HMGrunthos/CapInrushLimiter/CapInrush5-30V.asc

B1: bv; V=V(RCA,RCB)
C2: cap; 13200µF; V=50 Rser=0.03
C3: cap; 13200µF; V=50 Rser=0.03
C6: cap; 100nF; V=60
C7: cap; 100e-6
C10: cap; 16200µF; V=80 Rser=0.016
C11: cap; 680e-9
C12: cap; 10e-6
D1: diode; UF5406
D2: zener; BZX84B9V1LY
D3: zener; bzx55c24
D4: schottky; RB238NS150
D5: diode; BAS16H
D6: schottky; RB238NS150
D7: schottky; RB238NS150
D8: schottky; RB238NS150
D9: schottky; RB238NS150
D10: schottky; RB238NS150
D11: schottky; RB238NS150
D12: schottky; RB238NS150
D13: zener; BZX84B9V1LY
D14: diode; BAS16H
D15: diode; BAS16H
D19: zener; BZX84C15L
I1: current; PWL(0 0 4 0 9 7)
L2: ind; 1e-6; Rser=1600
M1: pmos; irf9540npbf
M4: pmos; BSP230
Q2: npn; KST42
Q3: npn; TIP41C
R1: res; R=if(time<0.1,1e9,1e-6)
R3: res; 37.36
R4: res; 0.0855
R5: res; 0.0855
R6: res; 0.0855
R7: res; 0.0855
R9: res; 10e3
R10: res; 8.3e3
R11: res; 43e3
R12: res; 100e3
R15: res; 3.5e3
R17: res; 100e3
R20: res; R=if((time<0.1)|((time > 3.5)&(time<4.5)),1e9,1e-6)
S1: sw; Relay
U1: LM4041_N_ADJ
V2: voltage; SINE(0 37.7736 50 0 0 0 2000)
V3: voltage; SINE(0 37.7736 50 0 0 0 2000)
Named nets: 0, T, S, RCA, RCB
.tran 0 10 0.102 startup
.model UF5406 d(is = 1.15563E-005 n = 3.45 rs = 0.0887337 eg = 1.11 xti = 3 cjo = 9.14327E-011 vj = 0.298558 m = 0.347605 fc = 0.5  tt = 1.57227E-007 bv = 660 ibv = 0.3 af = 1 kf = 0)
.inc Infineon-Spice-File-IRF9540NPBF-SM-v01_00-EN.spi
.options cshunt=1e-15
.inc BAS16H.txt
.inc BSP230.prm
.model Relay SW(Roff=1Meg Ron=1e-3 Vt=18V Vh=1)
.lib KST42.lib
.inc LM4041_N_ADJD1P233_TRANS.lib
.MODEL TIP41C NPN (IS=7.55826e-11 BF=260.542 NF=1.11221 VAF=100 IKF=0.526814
+ISE=1e-08 NE=2.18072 BR=26.0542 NR=1.5 VAR=1000 IKR=3.54059 ISC=1e-08
+NC=1.63849 RB=4.56157 IRB=0.1 RBM=0.1 RE=0.0162111 RC=0.0810556 XTB=0.1
+XTI=1 EG=1.206 CJE=1.93296e-10 VJE=0.4 MJE=0.259503 TF=1e-08 XTF=4.06972
+VTF=7.1157 ITF=0.001 CJC=1.09657e-10 VJC=0.730921 MJC=0.23 XCJC=0.803085 
+FC=0.8 TR=9.01013e-08 PTF=0 Vceo=100 ICrating=6 mfg=ON_Semi)
.lib BZX55C24.lib
