HMGrunthos/CapInrushLimiter/CapInrush5.asc

B1: bv; V=V(RCA,RCB)
C2: cap; 13200µF; V=50 Rser=0.03
C3: cap; 13200µF; V=50 Rser=0.03
C5: cap; 100e-9
C7: cap; 10e-6
C10: cap; 16200µF; V=80 Rser=0.016
C11: cap; 680e-9
C12: cap; 10e-6
D1: diode; UF5406
D2: zener; BZX84B9V1LY
D3: diode; 1N4001
D4: schottky; RB238NS150
D5: diode; BAS16H
D6: schottky; RB238NS150
D7: schottky; RB238NS150
D8: schottky; RB238NS150
D9: schottky; RB238NS150
D10: schottky; RB238NS150
D11: schottky; RB238NS150
D12: schottky; RB238NS150
D13: zener; BZX84B9V1LY
D14: diode; BAS16H
D15: diode; BAS16H
D19: zener; BZX84C15L
D21: LED; REDLED
I1: current; PWL(0 0 4.5 0 9 7)
L2: ind; 1e-6; Rser=5760
M1: pmos; irf9540npbf
M4: pmos; BSP230
Q2: npn; KST42
Q3: npn; KST42
R1: res; R=if(time<0.1,1e9,1e-6)
R3: res; 100
R4: res; 0.0855
R5: res; 0.0855
R6: res; 0.0855
R7: res; 0.0855
R9: res; 100e3
R10: res; 8.3e3
R11: res; 100e3
R12: res; 200e3
R13: res; 1.5e3
R15: res; 3.5e3
R17: res; 100e3
R20: res; R=if((time<0.1)|((time > 3.5)&(time<4.5)),1e9,1e-6)
S1: sw; Relay
V2: voltage; SINE(0 37.7736 50 0 0 0 2000)
V3: voltage; SINE(0 37.7736 50 0 0 0 2000)
Named nets: 0, T, S, RCA, RCB
.tran 10 startup
.model UF5406 d(is = 1.15563E-005 n = 3.45 rs = 0.0887337 eg = 1.11 xti = 3 cjo = 9.14327E-011 vj = 0.298558 m = 0.347605 fc = 0.5  tt = 1.57227E-007 bv = 660 ibv = 0.3 af = 1 kf = 0)
.inc Infineon-Spice-File-IRF9540NPBF-SM-v01_00-EN.spi
.options cshunt=1e-15
.inc BAS16H.txt
.inc BSP230.prm
.model 1N4001 D(Is=14.11n N=1.984 Rs=33.89m Ikf=94.81 Xti=3 Eg=1.11 Cjo=25.89p M=.44 Vj=.3245 Fc=.5 Bv=75 Ibv=10u Tt=5.7u Iave=1 Vpk=50 mfg=GI type=silicon
.model Relay SW(Roff=1Meg Ron=1e-3 Vt=34V Vh=2)
.lib KST42.lib
.MODEL REDLED D (IS=93.2P RS=42M N=3.73 BV=4 IBV=10U CJO=2.97P VJ=.75 M=.333 TT=4.32U)
