HMGrunthos/CapInrushLimiter/CapInrush1.asc

C1: cap; 16200µF; V=80
C2: cap; 10e-6
C3: cap; 680e-9
C4: cap; 13200µF; V=50
C5: cap; 13200µF; V=50
C6: cap; 100nF; V=60
D2: diode; BAS16H
D4: schottky; RB238NS150
D6: schottky; RB238NS150
D7: schottky; RB238NS150
D8: schottky; RB238NS150
D9: schottky; RB238NS150
D10: schottky; RB238NS150
D11: schottky; RB238NS150
D12: schottky; RB238NS150
D13: diode; 1N4001
D14: zener; NZX3V9C
D15: zener; NZX5V6C
D16: zener; BZX84C15L
L1: ind; 1e-6; Rser=1.6e3
M2: pmos; BSP230
M3: pmos; irf9540npbf
Q2: npn; ZTX450
R1: res; 8.5e0
R2: res; 47e3
R3: res; 3.3e3
R4: res; 0.0855
R5: res; 0.0855
R6: res; 0.0855
R7: res; 0.0855
R8: res; 10e3
R11: res; 4.7e6
R17: res; 22e3
V1: voltage; 0
V2: voltage; SINE(0 37.7736 50 0 0 0 2000)
V3: voltage; SINE(0 37.7736 50 0 0 0 2000)
Named nets: 0
.tran 5 startup
.model uf5406 d(is = 1.15563E-005 n = 3.45 rs = 0.0887337 eg = 1.11 xti = 3 cjo = 9.14327E-011 vj = 0.298558 m = 0.347605 fc = 0.5  tt = 1.57227E-007 bv = 660 ibv = 0.3 af = 1 kf = 0)
.inc NZX5V6C.prm
.inc NZX3V9C.prm
.inc Infineon-Spice-File-IRF9540NPBF-SM-v01_00-EN.spi
.options cshunt=1e-15
.MODEL ZTX450 NPN IS =3.941445E-14 BF =175 VAF=109.45 NF =1 IKF=.8 ISE=7.4025E-15 NE =1.3 BR =20.5 VAR=14.25 NR =.974 IKR=.1 ISC=3.157E-13 NC =1.2 RB =1.1 RE =.1259 RC =.0539 CJE=63E-12 TF =.75E-9 CJC=15.8E-12 TR =85E-9 VJC=.505 MJC=.39
.inc BAS16H.txt
.inc BSP230.prm
.model 1N4001 D(Is=14.11n N=1.984 Rs=33.89m Ikf=94.81 Xti=3 Eg=1.11 Cjo=25.89p M=.44 Vj=.3245 Fc=.5 Bv=75 Ibv=10u Tt=5.7u Iave=1 Vpk=50 mfg=GI type=silicon
